JordanAceto/rust_ribbon_controller/hardware/main_pcb/docs/2D/ribbon_controller_B.Cu.pdf

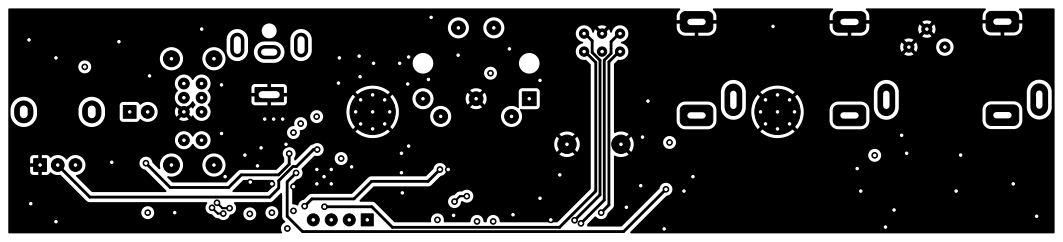
[picture p13: page 1]

File: ribbon_controller.kicad_pcb Sheet: creativecommons.org/licenses/by/4.0

Id: 1/1 Title: Ribbon Controller Main Board
