JordanAceto/rust_ribbon_controller/hardware/faceplate/docs/2D/ribbon_controller_faceplate_B.Paste.pdf

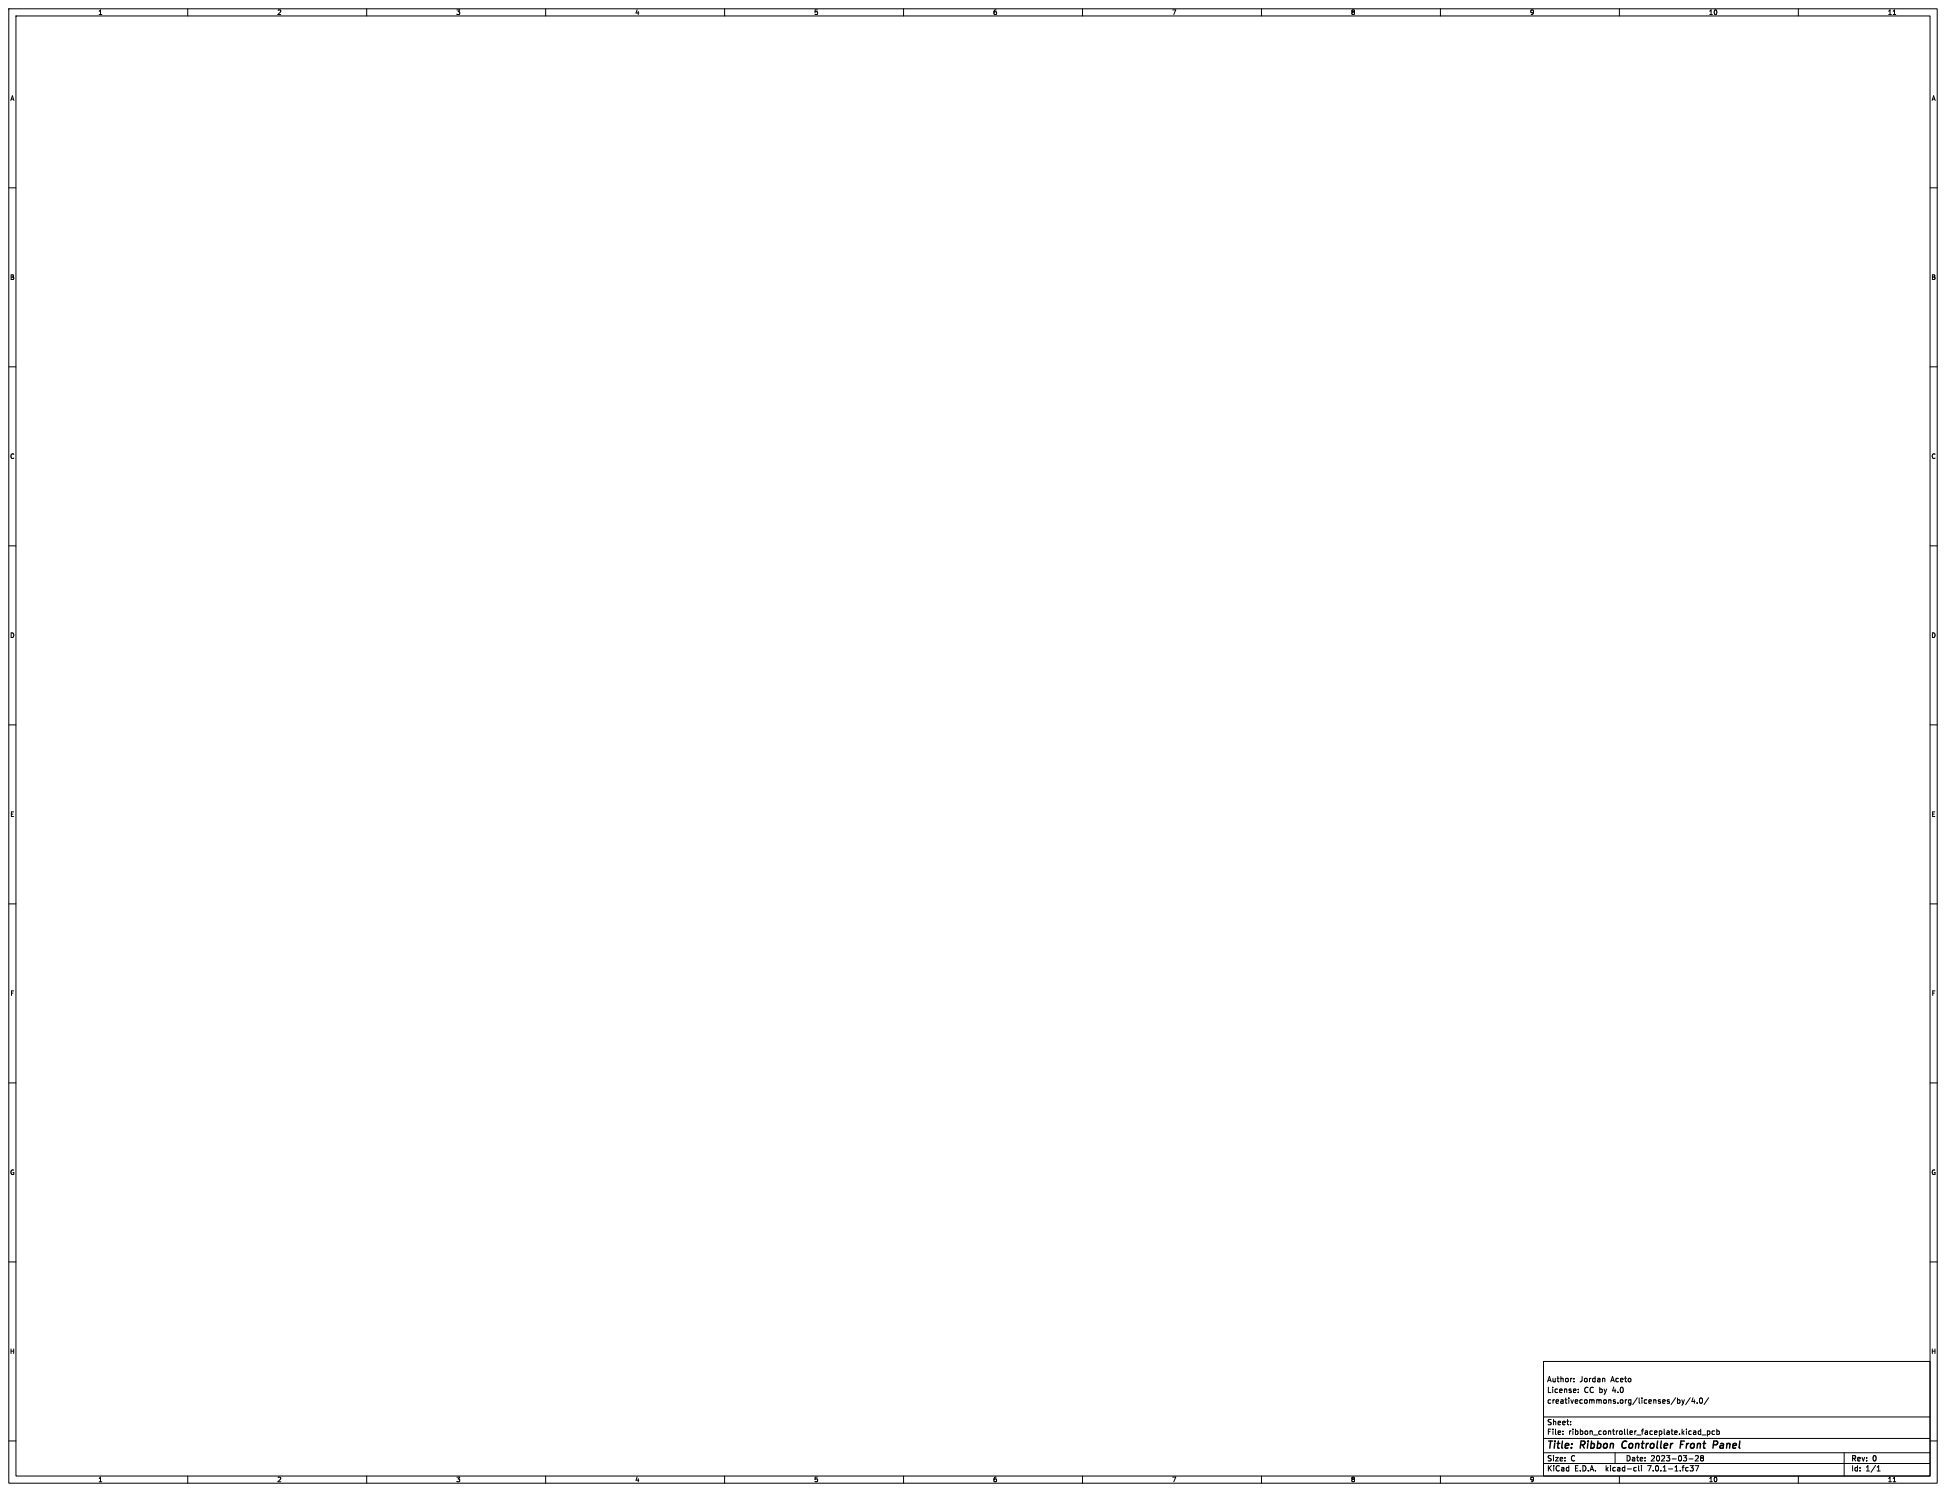
[picture p22: page 1]
