JordanAceto/rust_ribbon_controller/hardware/faceplate/docs/2D/ribbon_controller_faceplate_B.SilkS.pdf

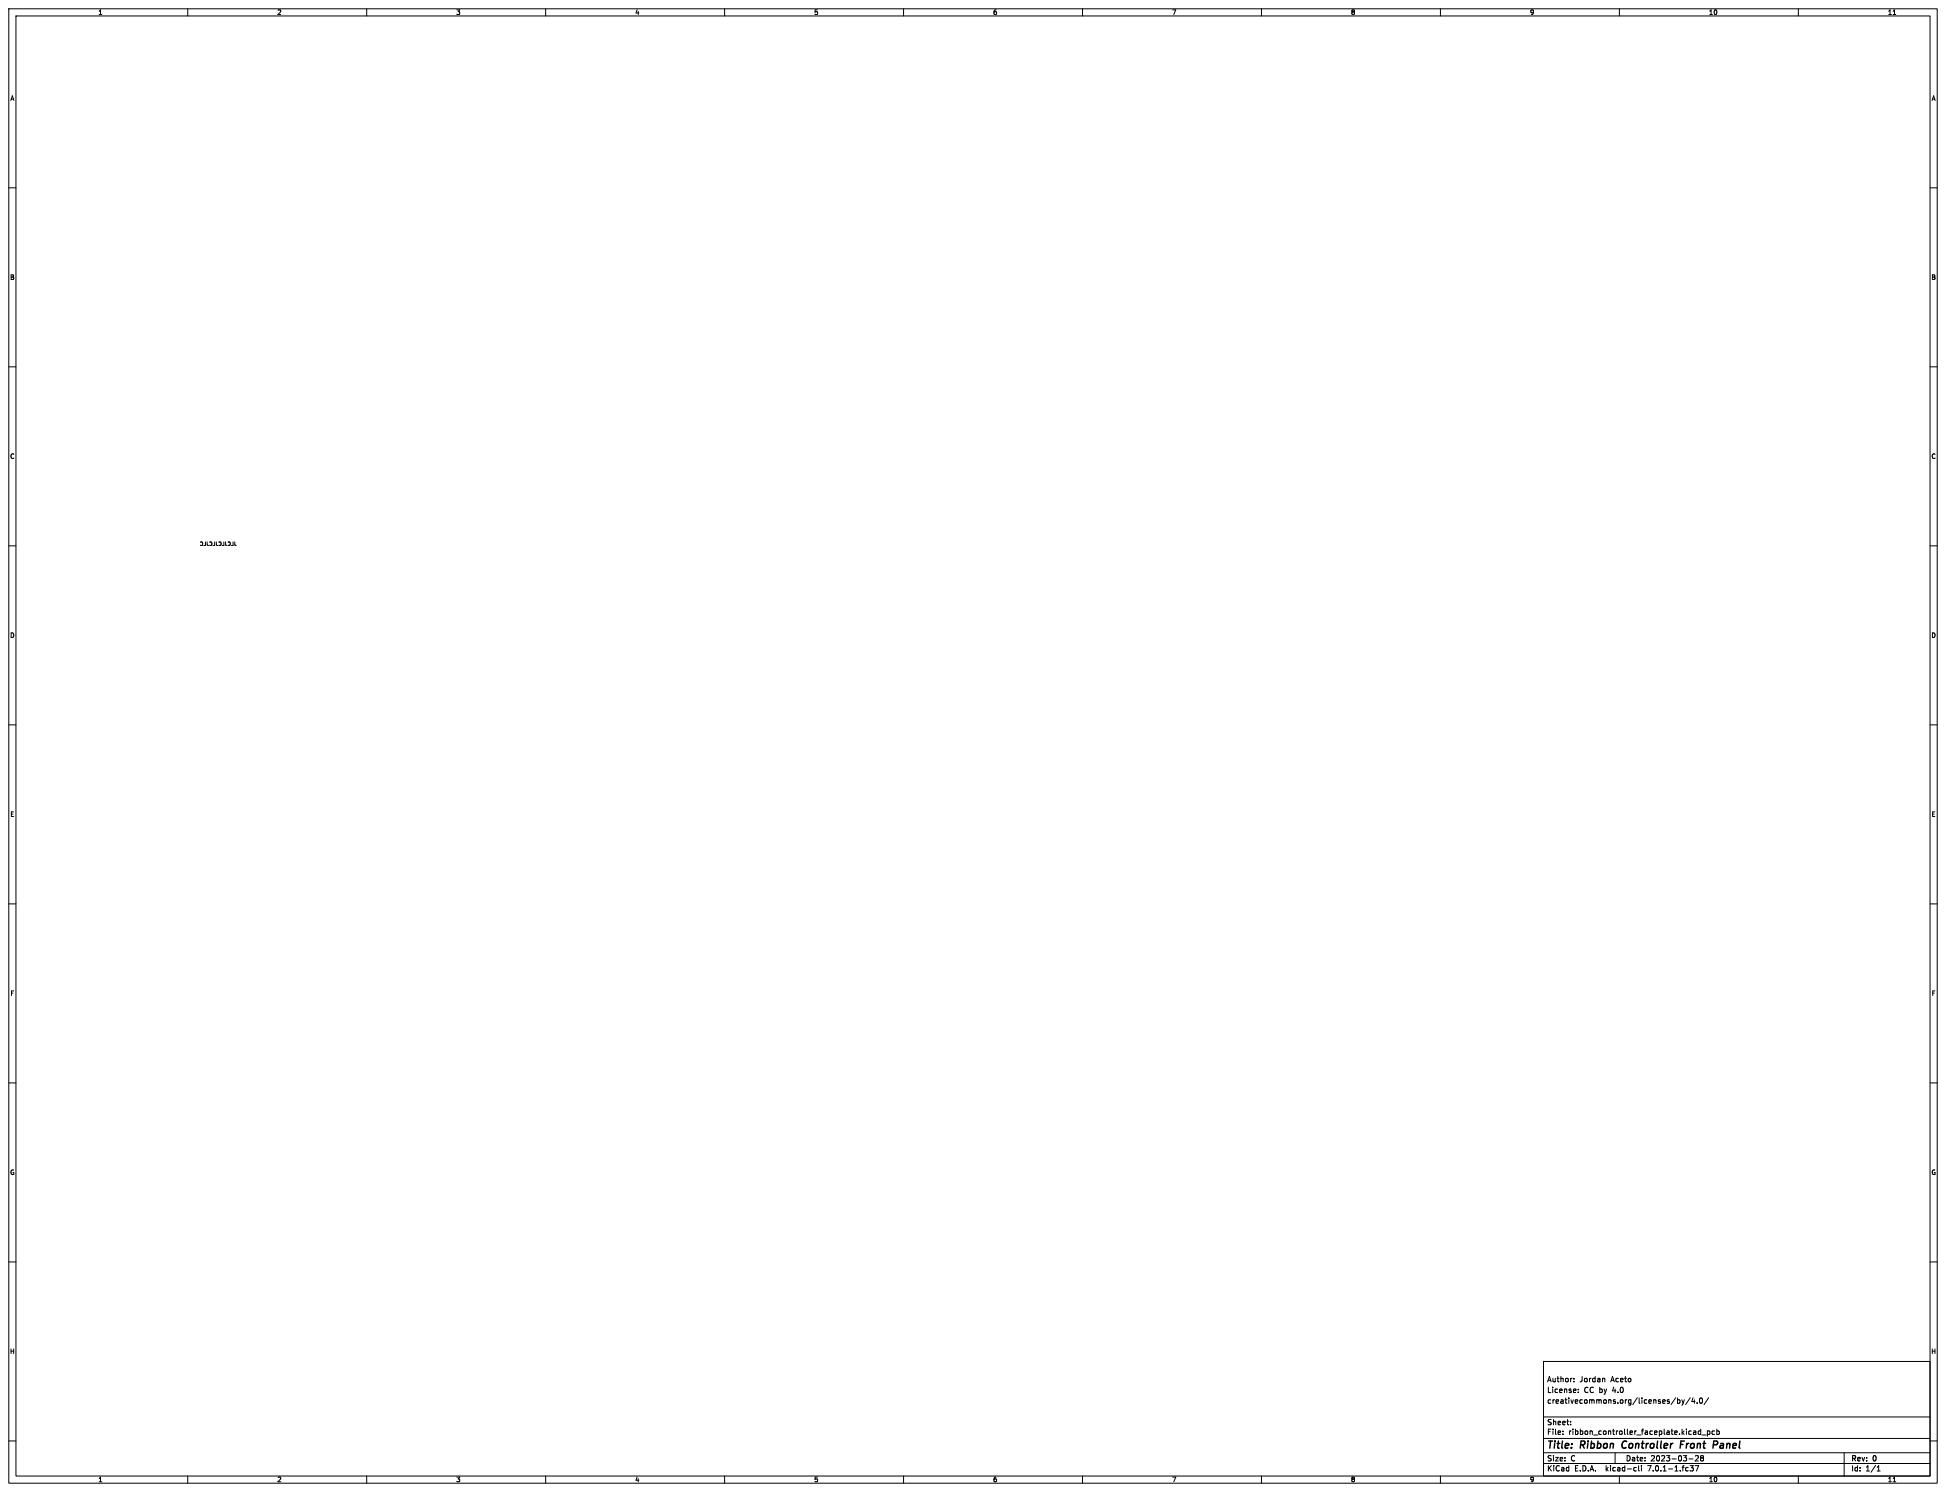
[picture p23: page 1]
