JordanAceto/rust_ribbon_controller/hardware/faceplate/docs/2D/ribbon_controller_faceplate_Edge.Cuts.pdf

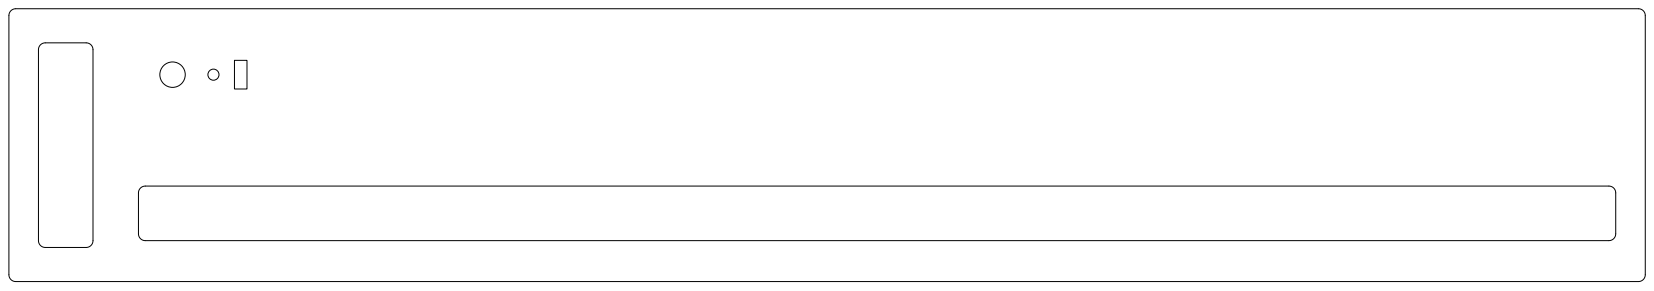
[picture p24: page 1]
