JordanAceto/rust_ribbon_controller/hardware/faceplate/docs/2D/ribbon_controller_faceplate_F.SilkS.pdf

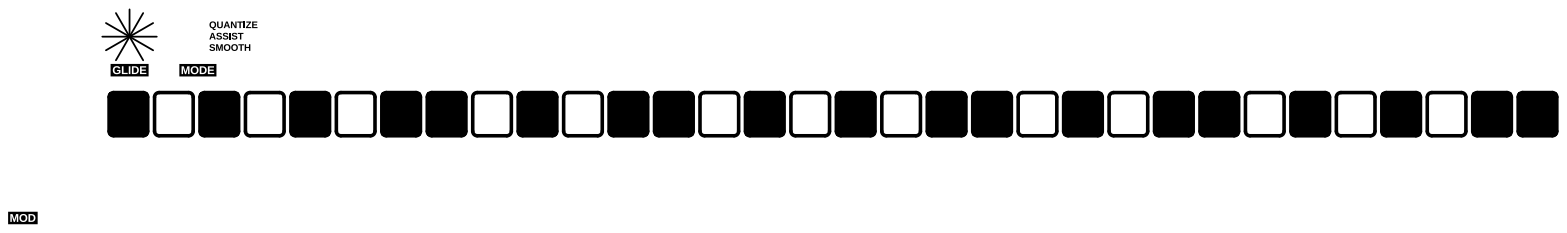
[picture p25: page 1]
